Nauman3S/Smart-Water-Pressure-Monitoring-System/artwork/scr1.png

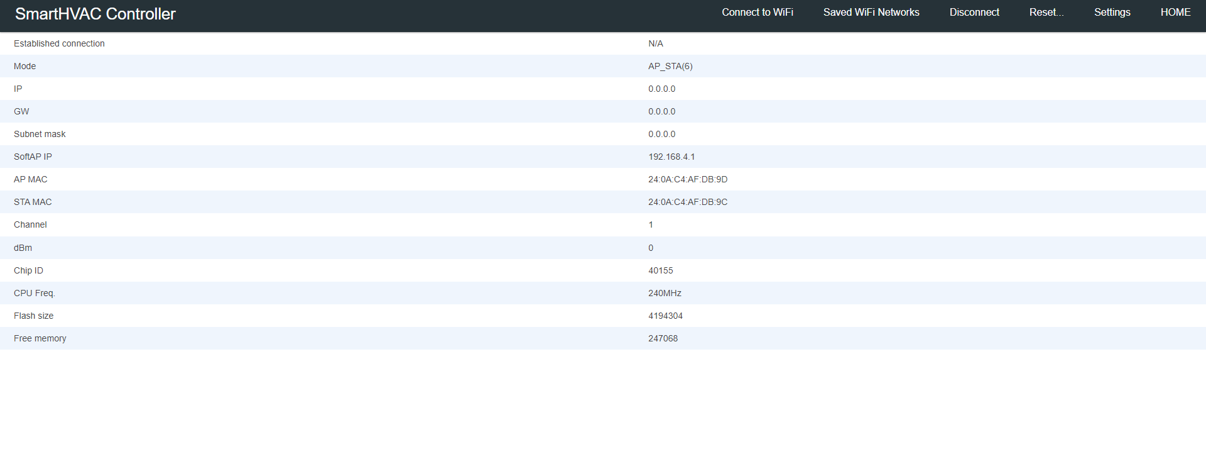
artwork/scr1.png
