Nauman3S/Smart-Water-Pressure-Monitoring-System/artwork/scr2.png

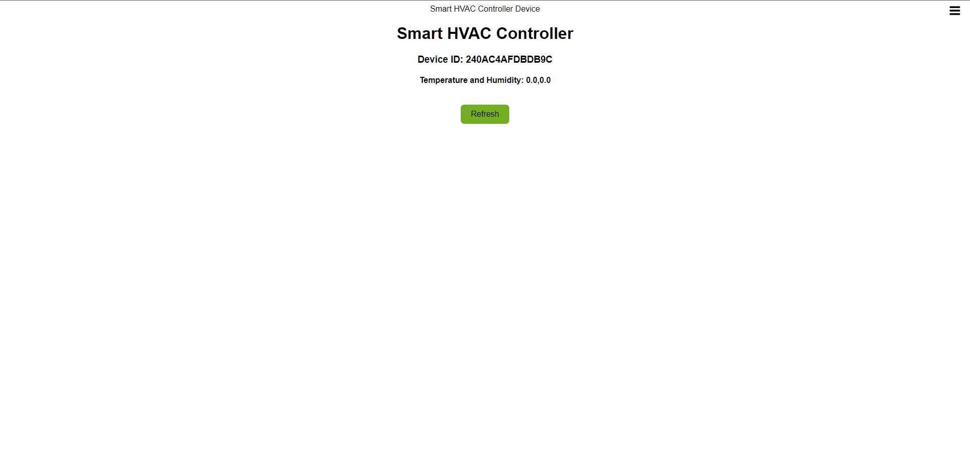
artwork/scr2.png
