Nauman3S/Smart-Water-Pressure-Monitoring-System/Circuit/relay.jpg

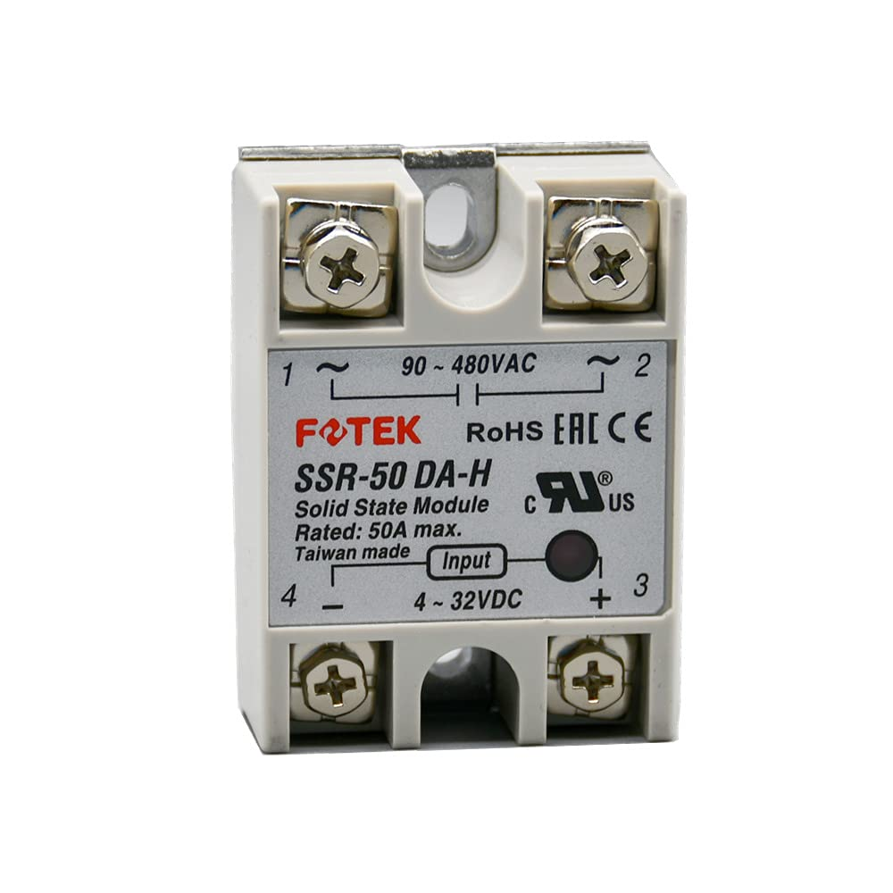
Circuit/relay.jpg
