Nauman3S/Smart-Water-Pressure-Monitoring-System/Circuit/sim7000g.jpg

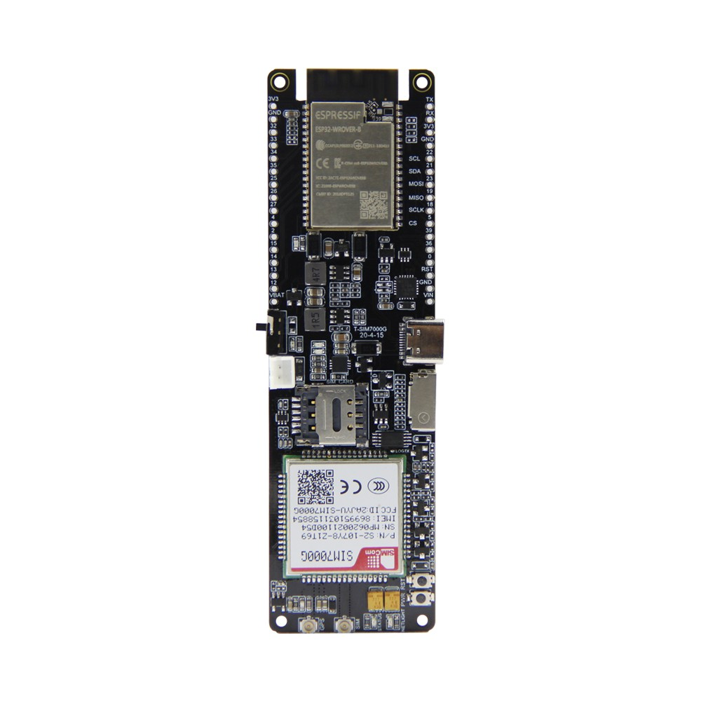
Circuit/sim7000g.jpg
