Nauman3S/Smart-Water-Pressure-Monitoring-System/Firmware/ads.h

#include <Adafruit_ADS1X15.h>

//Adafruit_ADS1115 ads;  /* Use this for the 16-bit version */
Adafruit_ADS1015 ads; /* Use this for the 12-bit version */
uint8_t adsAvailable = 0;
void setupADS(void)
{
  //   Serial.begin(9600);
  //   Serial.println("Hello!");

  //   Serial.println("Getting single-ended readings from AIN0..3");
  //   Serial.println("ADC Range: +/- 6.144V (1 bit = 3mV/ADS1015, 0.1875mV/ADS1115)");

  // The ADC input range (or gain) can be changed via the following
  // functions, but be careful never to exceed VDD +0.3V max, or to
  // exceed the upper and lower limits if you adjust the input range!
  // Setting these values incorrectly may destroy your ADC!
  //                                                                ADS1015  ADS1115
  //                                                                -------  -------
  // ads.setGain(GAIN_TWOTHIRDS);  // 2/3x gain +/- 6.144V  1 bit = 3mV      0.1875mV (default)
  // ads.setGain(GAIN_ONE);        // 1x gain   +/- 4.096V  1 bit = 2mV      0.125mV
  // ads.setGain(GAIN_TWO);        // 2x gain   +/- 2.048V  1 bit = 1mV      0.0625mV
  // ads.setGain(GAIN_FOUR);       // 4x gain   +/- 1.024V  1 bit = 0.5mV    0.03125mV
  // ads.setGain(GAIN_EIGHT);      // 8x gain   +/- 0.512V  1 bit = 0.25mV   0.015625mV
  // ads.setGain(GAIN_SIXTEEN);    // 16x gain  +/- 0.256V  1 bit = 0.125mV  0.0078125mV

  if (!ads.begin())
  {
    Serial.println("Failed to initialize ADS.");
    adsAvailable = 0;
  }
  else
  {
    adsAvailable = 1;
  }
}

// void loop(void)
// {
//   int16_t adc0, adc1, adc2, adc3;
//   float volts0, volts1, volts2, volts3;

//   adc0 = ads.readADC_SingleEnded(0);
//   adc1 = ads.readADC_SingleEnded(1);
//   adc2 = ads.readADC_SingleEnded(2);
//   adc3 = ads.readADC_SingleEnded(3);

//   volts0 = ads.computeVolts(adc0);
//   volts1 = ads.computeVolts(adc1);
//   volts2 = ads.computeVolts(adc2);
//   volts3 = ads.computeVolts(adc3);

//   Serial.println("-----------------------------------------------------------");
//   Serial.print("AIN0: "); Serial.print(adc0); Serial.print("  "); Serial.print(volts0); Serial.println("V");
//   Serial.print("AIN1: "); Serial.print(adc1); Serial.print("  "); Serial.print(volts1); Serial.println("V");
//   Serial.print("AIN2: "); Serial.print(adc2); Serial.print("  "); Serial.print(volts2); Serial.println("V");
//   Serial.print("AIN3: "); Serial.print(adc3); Serial.print("  "); Serial.print(volts3); Serial.println("V");

//   delay(1000);
// }
const float OffSet = 0.483;
float V, P;
/************************************************************
  Water Sensor Key Parameter
  - Parts No.:KY-3-5
  - Sensing range: 0 - 1.6 MPa
  - Input Voltage: 5VDC
  - Output Voltage: 0.5 - 4.5 VDC
    (Linearly corresponding to 0 - 1.6 MPa)
  - Accuary: 0.5% - 1% FS
**************************************************************/

String getPressure()
{

  int16_t adc0, adc1, adc2, adc3;
  float volts0, volts1, volts2, volts3;
  if (adsAvailable == 1)
  {
    adc0 = ads.readADC_SingleEnded(0);
    volts0 = ads.computeVolts(adc0);
    //P = (volts0 - OffSet) * 400;
    P = map(volts0, 0.5, 4.5, 0, 1.6);
    return String(P);
  }
  else{
    return String("0");
  }
}
