Nauman3S/Smart-Water-Pressure-Monitoring-System/Firmware_WiFi/MQTTFuncs.h

void MQTTUnSubscribe();
void MQTTSubscriptions();
void callback(char *topic, byte *payload, unsigned int length);
void reconnect();
bool mqttConnect();
void mqttPublish(String path, String msg);
int deviceExisits = 0;
int ledStatus = 0;
void MQTTUnSubscribe()
{
    //String topicN = String("CPT/device/price");

    mqttClient.unsubscribe(topicRelay);
}
void MQTTSubscriptions()
{
    //mqttClient.subscribe("SmartTControl/data/v");

    // for(int i=0;i<10;i++){
    //   IMEIsList[i]==String("NA");
    // }
    //String topicN = String("CPT/device/price");

    mqttClient.subscribe(topicRelay);
}
void callback(char *topic, byte *payload, unsigned int length)
{
    Serial.print("Message arrived [");
    Serial.print(topic);
    Serial.print("] ");
    String pLoad = "";
    for (int i = 0; i < length; i++)
    {
        Serial.print((char)payload[i]);
        pLoad = pLoad + String((char)payload[i]);
    }
    Serial.println();
    if (String(topic) == topicRelay)
    {
        ledStatus = !ledStatus;
        digitalWrite(LED_PIN, ledStatus);
        if (pLoad.indexOf(String("ON")) >= 0)
        {
            digitalWrite(RELAY_PIN, 1);
        }
        else
        {
            digitalWrite(RELAY_PIN, 0);
        }
        //mqtt.publish(topicPressureSensorStatus, ledStatus ? "1" : "0");
    }

    pLoad = "";
}
void reconnect()
{
    // Loop until we're reconnected
    while (!mqttClient.connected())
    {
        Serial.print("Attempting MQTT connection...");
        // Create a random client ID
        String clientId = "ESP32Client-";
        clientId += String(random(0xffff), HEX);
        // Attempt to connect
        if (mqttClient.connect(clientId.c_str(), mqtt_user, mqtt_pass))
        {
            Serial.println("Established:" + String(clientId));
            //mqttClient.subscribe("SmartTControl/data/v");
            MQTTSubscriptions();
            // return true;
        }
        else
        {
            Serial.print("failed, rc=");
            Serial.print(mqttClient.state());
            Serial.println(" try again in 5 seconds");
            // Wait 5 seconds before retrying
            delay(5000);
        }
    }
}
bool mqttConnect()
{
    static const char alphanum[] = "0123456789"
                                   "ABCDEFGHIJKLMNOPQRSTUVWXYZ"
                                   "abcdefghijklmnopqrstuvwxyz"; // For random generation of client ID.
    char clientId[9];

    uint8_t retry = 3;
    while (!mqttClient.connected())
    {
        if (String(mqtt_server).length() <= 0)
            break;

        mqttClient.setServer(mqtt_server, 1883);
        mqttClient.setCallback(callback);
        Serial.println(String("Attempting MQTT broker:") + String("HiveMQ Broker"));
        internetStatus = "Connecting...";

        for (uint8_t i = 0; i < 8; i++)
        {
            clientId[i] = alphanum[random(62)];
        }
        clientId[8] = '\0';

        if (mqttClient.connect(clientId, mqtt_user, mqtt_pass))
        {
            Serial.println("Established:" + String(clientId));
            internetStatus = "Connected";
            //mqttClient.subscribe("SmartTControl/data/v");
            MQTTSubscriptions();
            return true;
        }
        else
        {
            Serial.println("Connection failed:" + String(mqttClient.state()));
            internetStatus = "Not-Connected. Retrying...";
            if (!--retry)
                break;
            delay(3000);
        }
    }
    return false;
}

void mqttPublish(String path, String msg)
{
    //String path = String("channels/") + channelId + String("/publish/") + apiKey;
    mqttClient.publish(path.c_str(), msg.c_str());
}
